bellabaohaha/CITS5206-Gp2/Deliverables/Prototype/LoRa Gateway Prototype.pdf

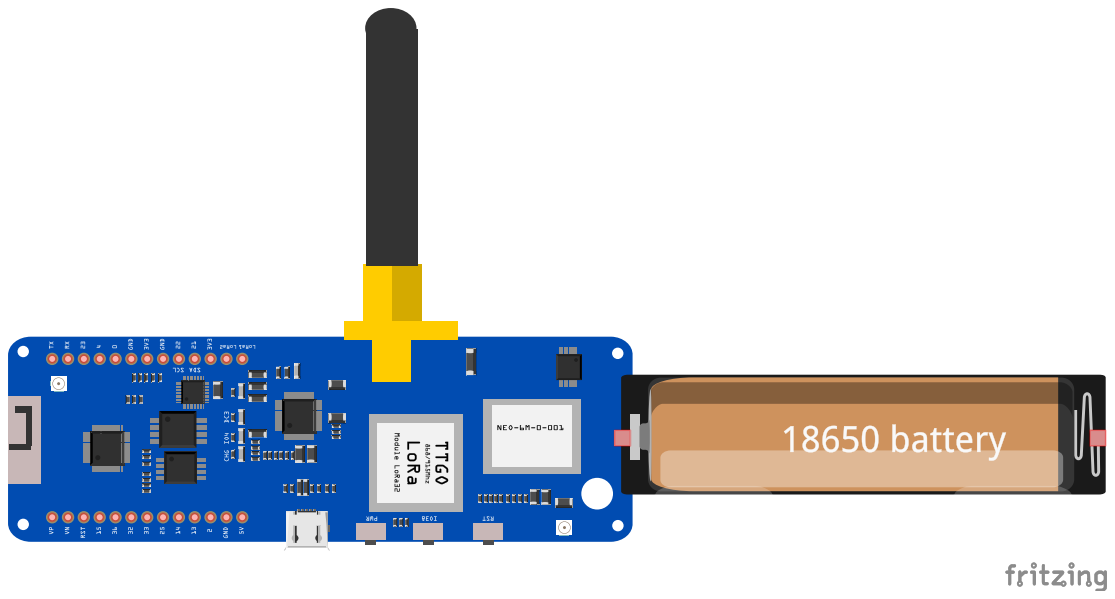
[picture p14: page 1]
