bellabaohaha/CITS5206-Gp2/Deliverables/Prototype/Soil Moisture IoT Prototype.pdf

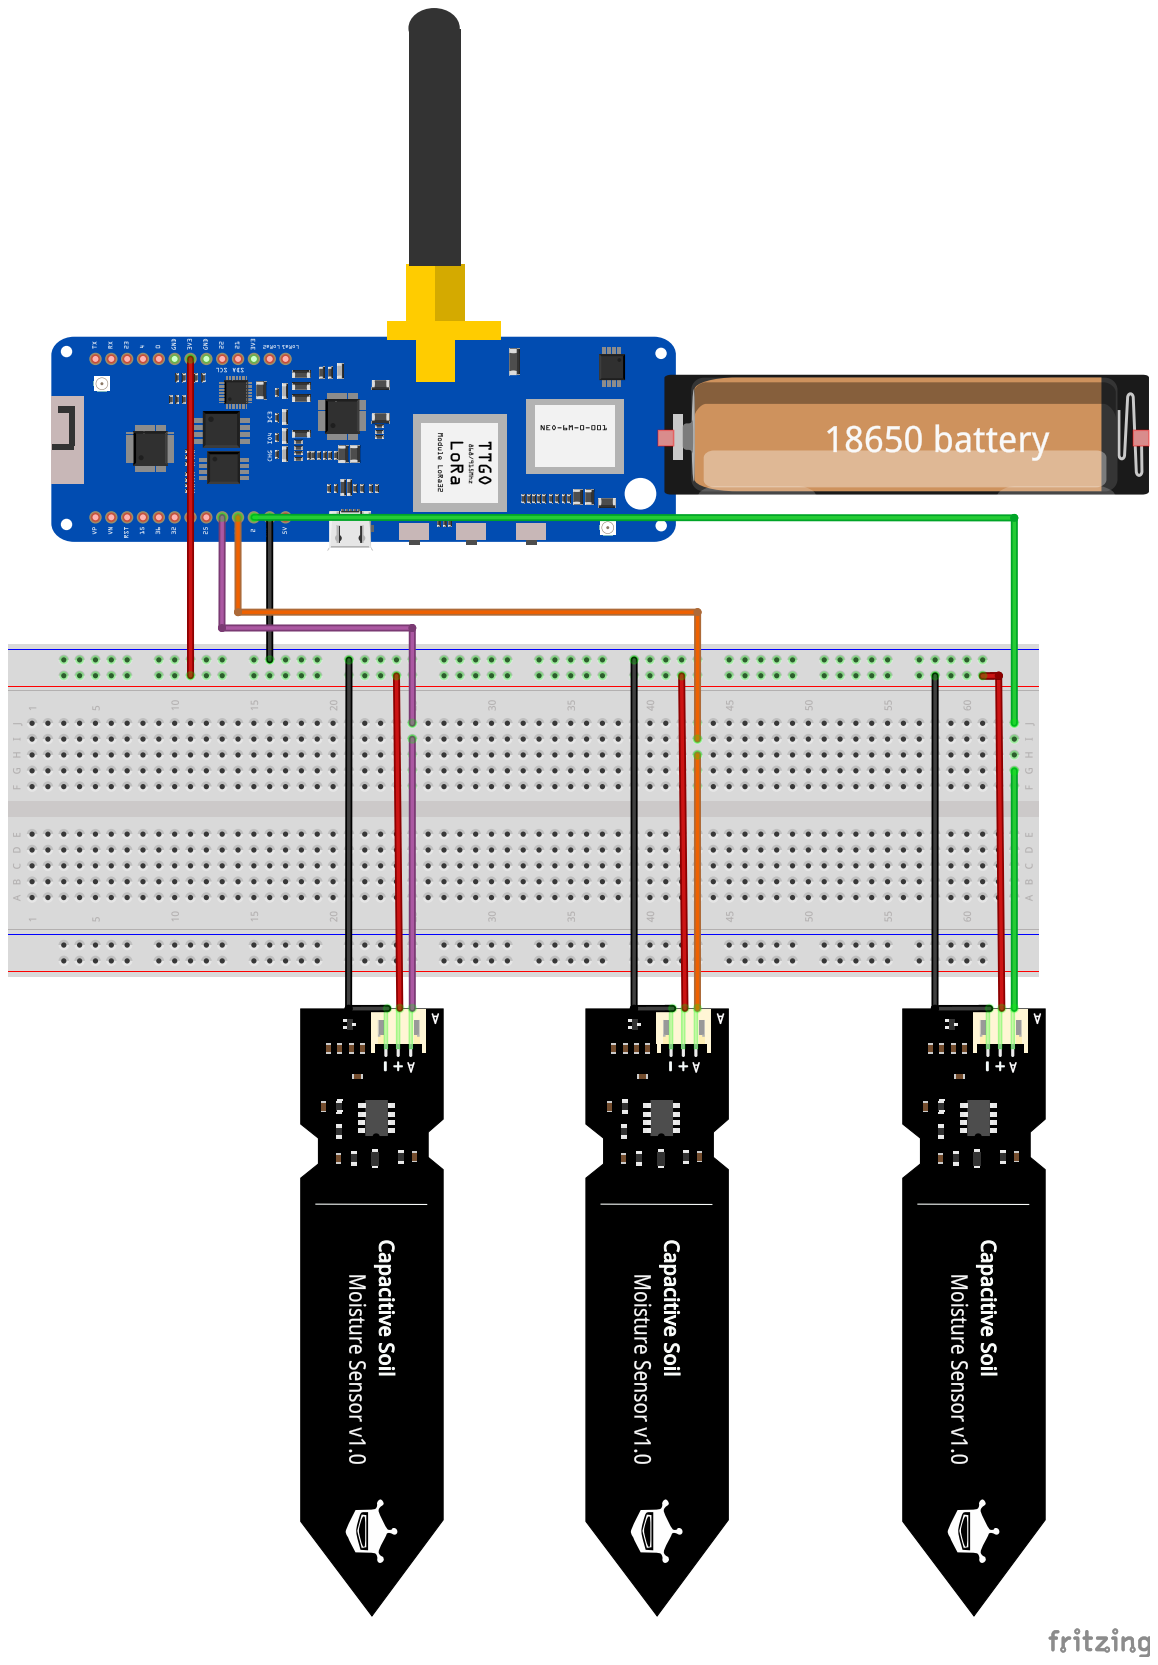
[picture p15: page 1]
